denjhang/OPN-OPLL-MegaMod/OPN+OPLL AMP v0.1/pics/sshot-20231009-171946.png

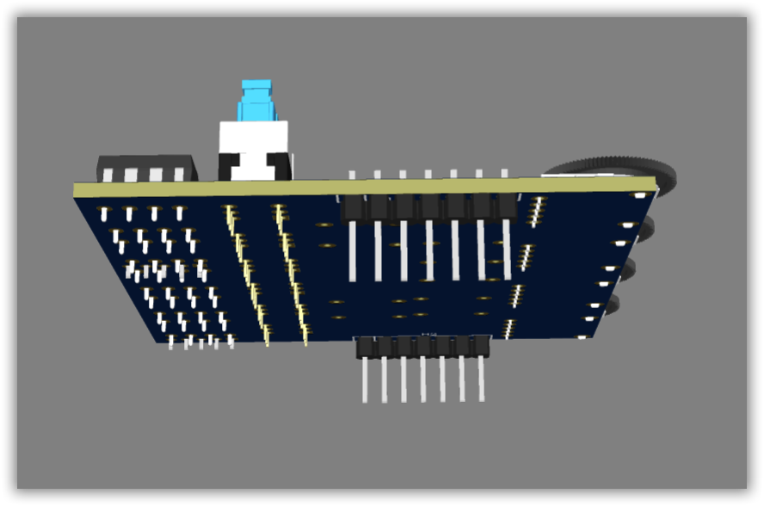
OPN+OPLL AMP v0.1/pics/sshot-20231009-171946.png
