denjhang/OPN-OPLL-MegaMod/OPN+OPLL AMP v0.1/pics/sshot-20231009-214024.png

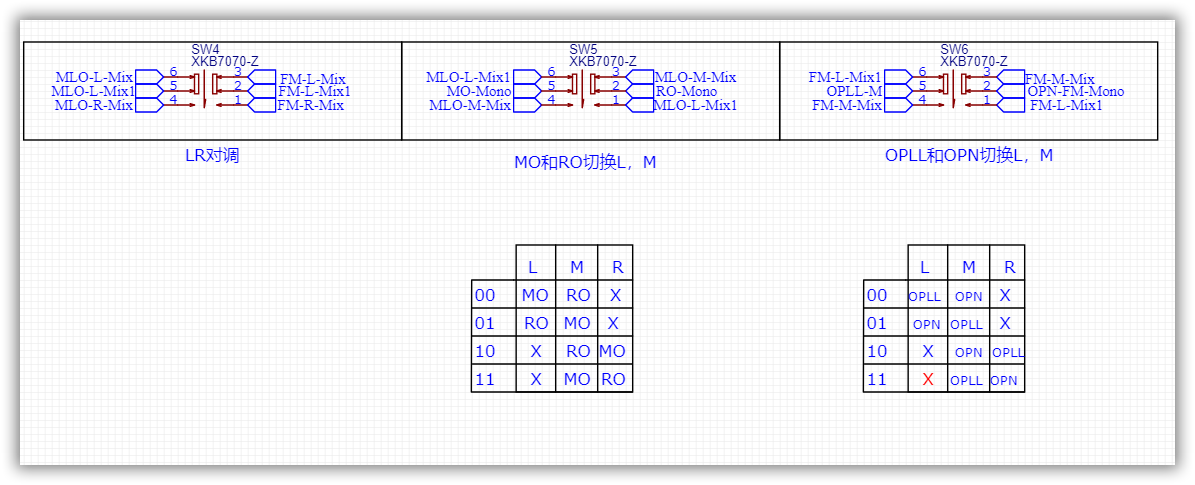
OPN+OPLL AMP v0.1/pics/sshot-20231009-214024.png
