denjhang/OPN-OPLL-MegaMod/OPN+OPLL AMP v0.1/pics/sshot-20231010-000824.png

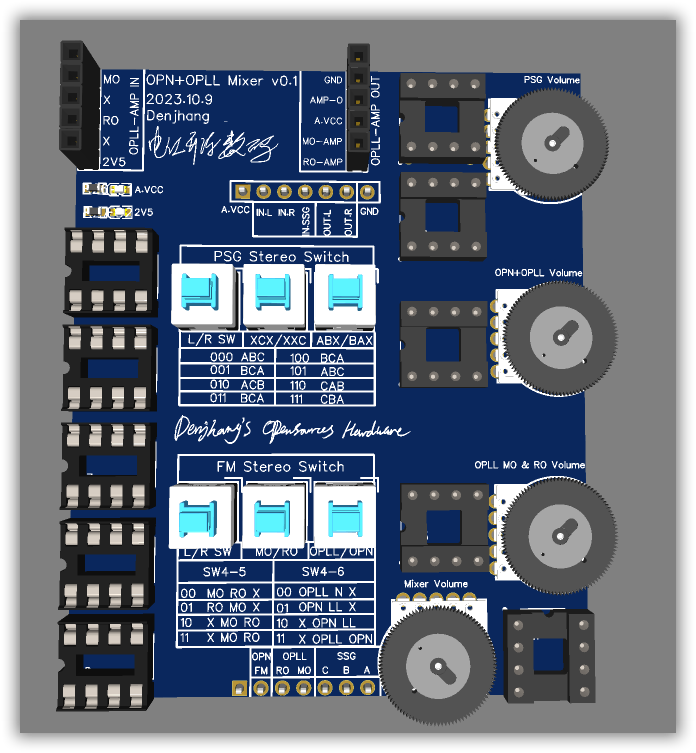
OPN+OPLL AMP v0.1/pics/sshot-20231010-000824.png
