denjhang/OPN-OPLL-MegaMod/OPN+OPLL Mixer v0.2/sshot-20231104-174121.png

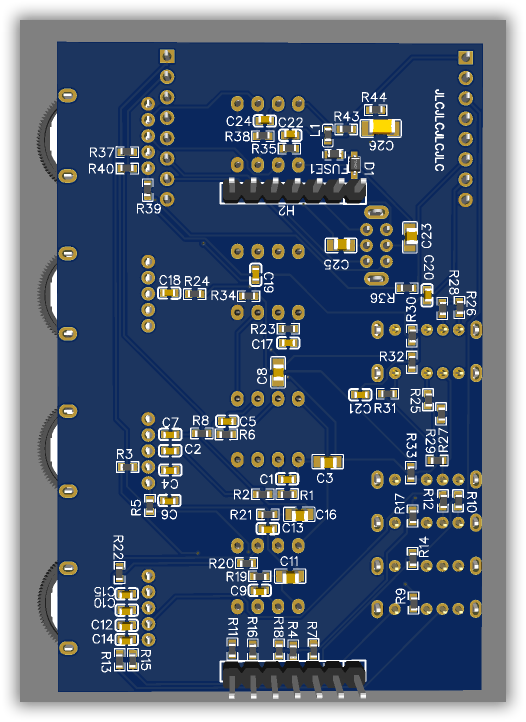
OPN+OPLL Mixer v0.2/sshot-20231104-174121.png
