denjhang/OPN-OPLL-MegaMod/pics/sshot-20231008-172245.png

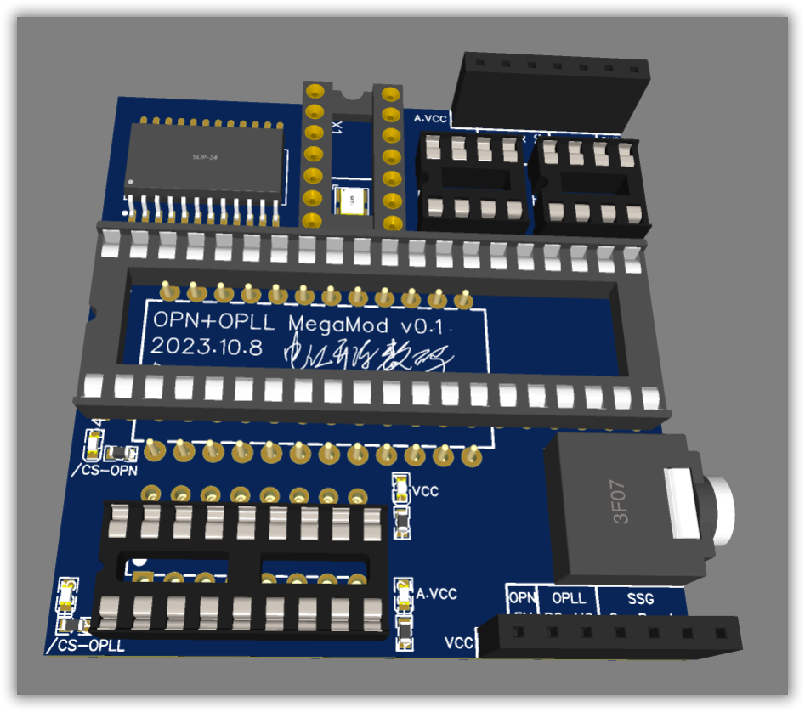
pics/sshot-20231008-172245.png
