denjhang/OPN-OPLL-MegaMod/pics/sshot-20231008-172254.png

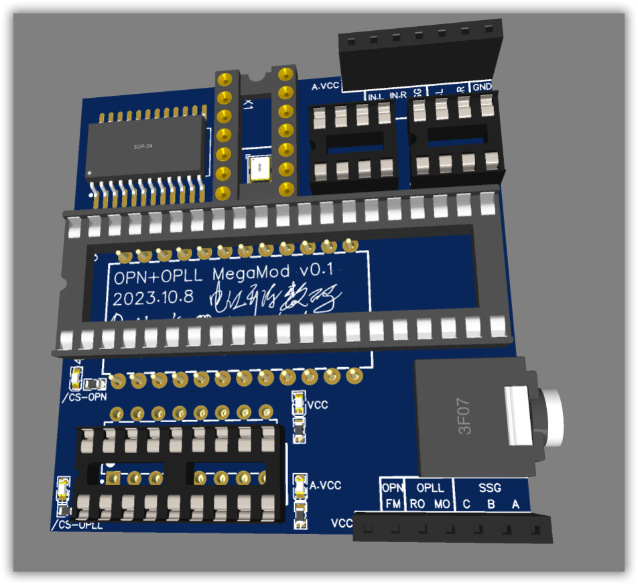
pics/sshot-20231008-172254.png
