denjhang/OPN-OPLL-MegaMod/pics/sshot-20231008-172621.png

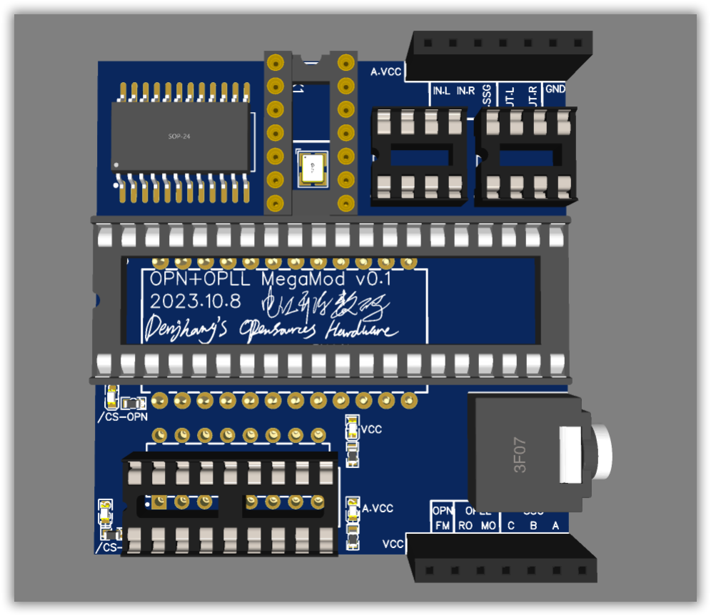
pics/sshot-20231008-172621.png
