denjhang/OPN-OPLL-MegaMod/pics/sshot-20231008-172805.png

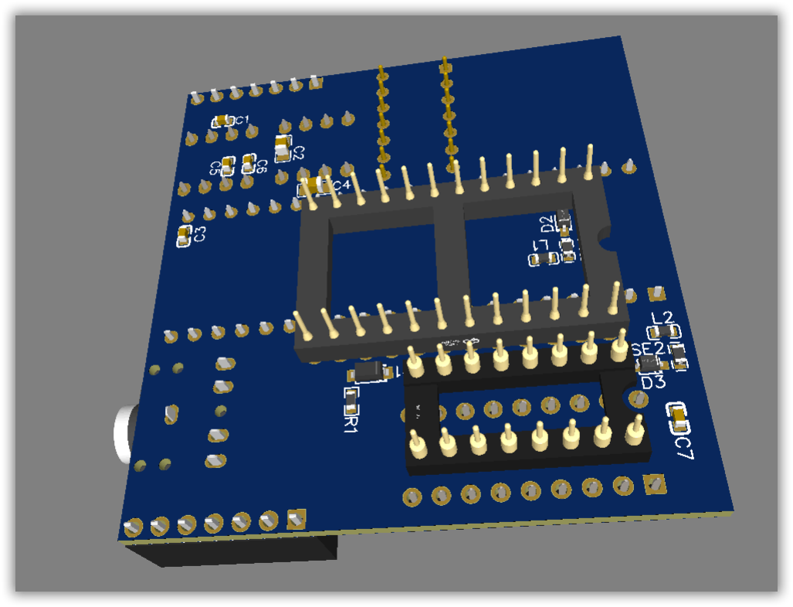
pics/sshot-20231008-172805.png
