denjhang/OPN-OPLL-MegaMod/pics/sshot-20231008-173001.png

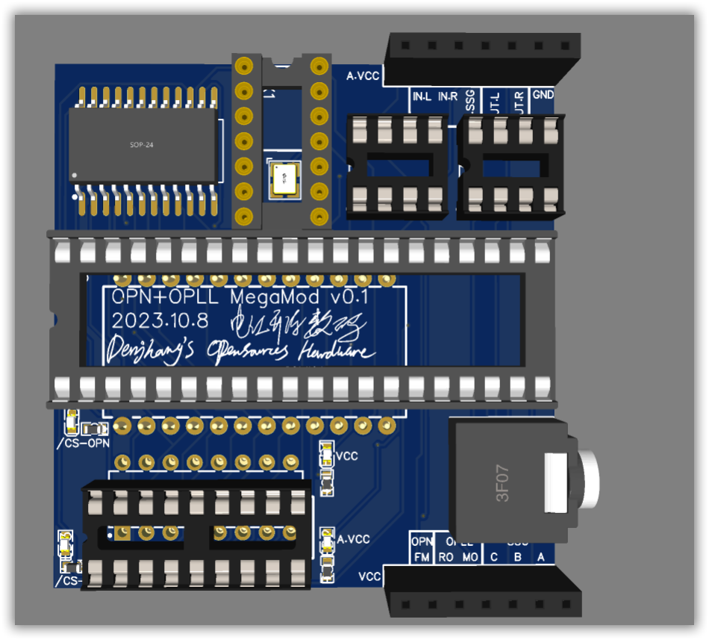
pics/sshot-20231008-173001.png
