denjhang/OPN-OPLL-MegaMod/pics/sshot-20231008-173020.png

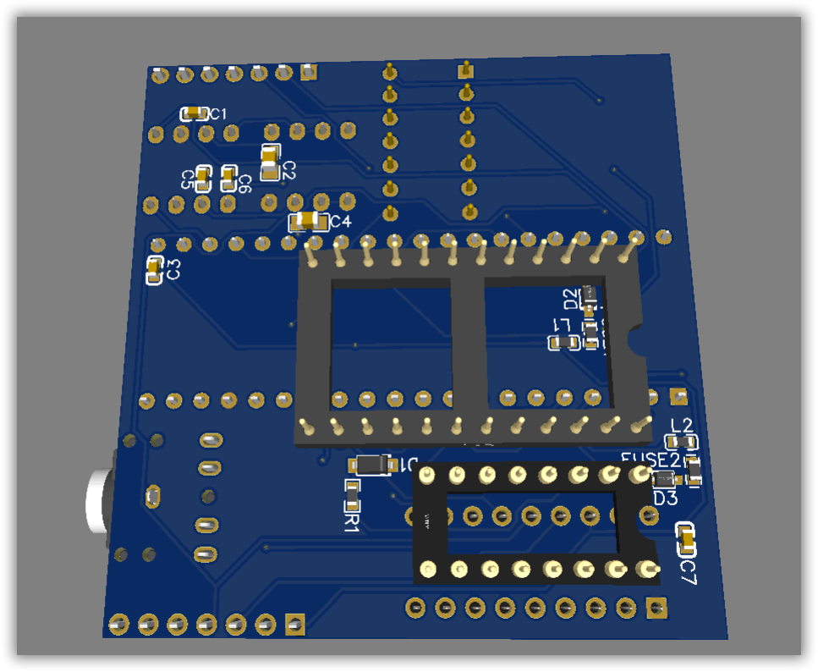
pics/sshot-20231008-173020.png
