denjhang/OPN-OPLL-MegaMod/资料2/5V 5X preamp.png

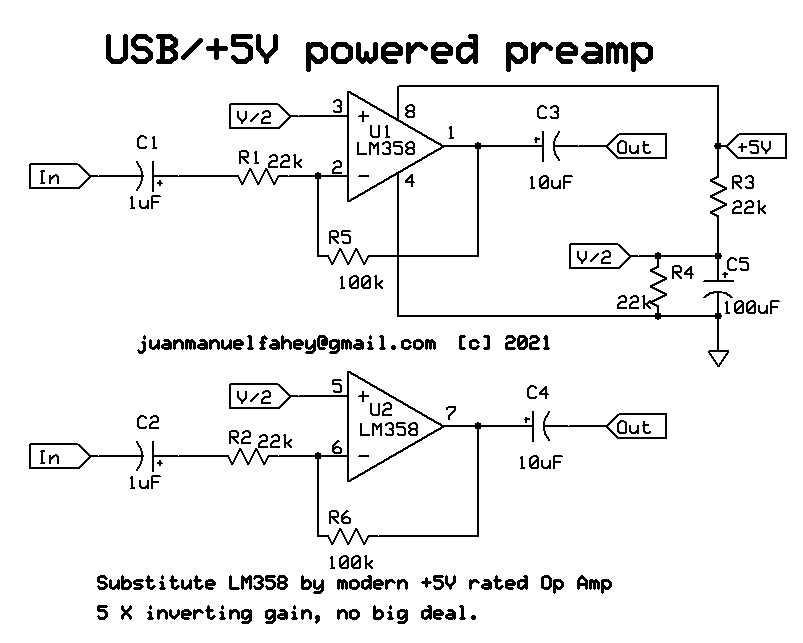
资料2/5V 5X preamp.png
