denjhang/OPN-OPLL-MegaMod/资料2/amplifier-amp112.gif

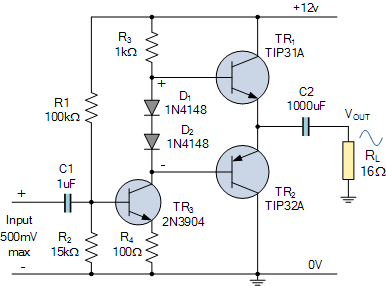
资料2/amplifier-amp112.gif
