denjhang/OPN-OPLL-MegaMod/资料2/flxtU.png

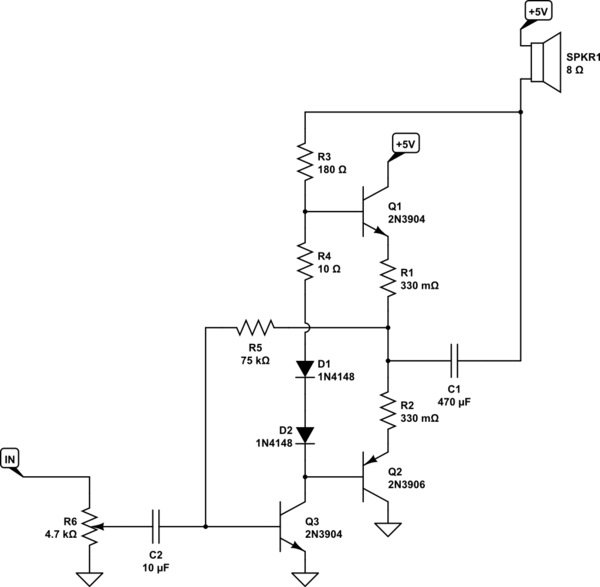
资料2/flxtU.png
