denjhang/OPN-OPLL-MegaMod/资料2/fm_hat_turbo1.0-f.jpg

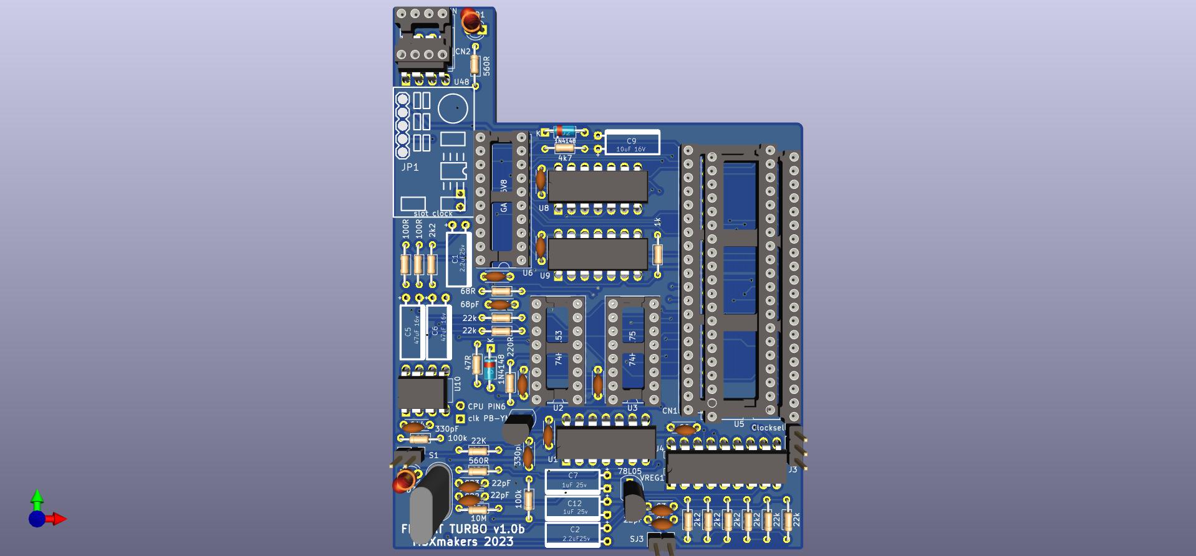
资料2/fm_hat_turbo1.0-f.jpg
