denjhang/OPN-OPLL-MegaMod/资料2/Fva4u.png

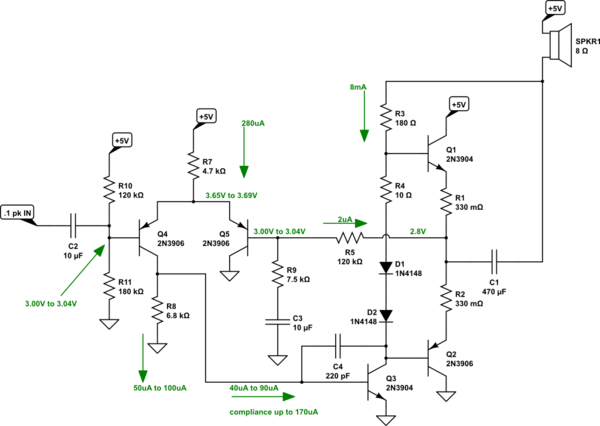
资料2/Fva4u.png
