denjhang/OPN-OPLL-MegaMod/资料2/QDV9V.jpg

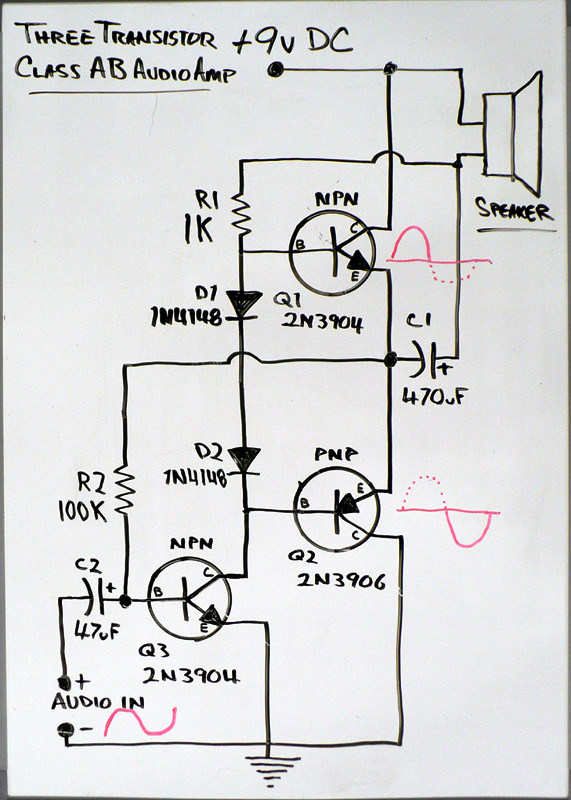
资料2/QDV9V.jpg
