denjhang/OPN-OPLL-MegaMod/资料3/6f60fb1f44.jpg

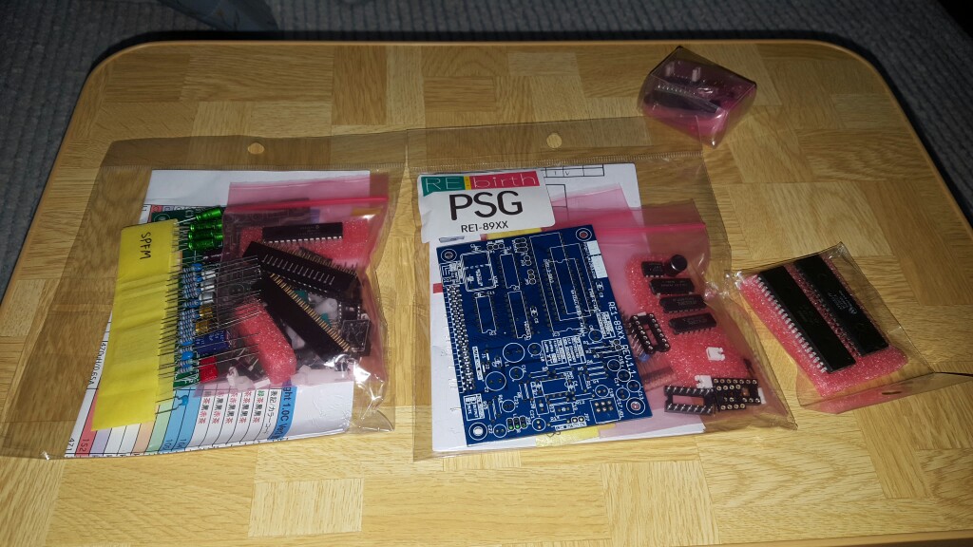
资料3/6f60fb1f44.jpg
