denjhang/OPN-OPLL-MegaMod/资料3/0962512435.jpg

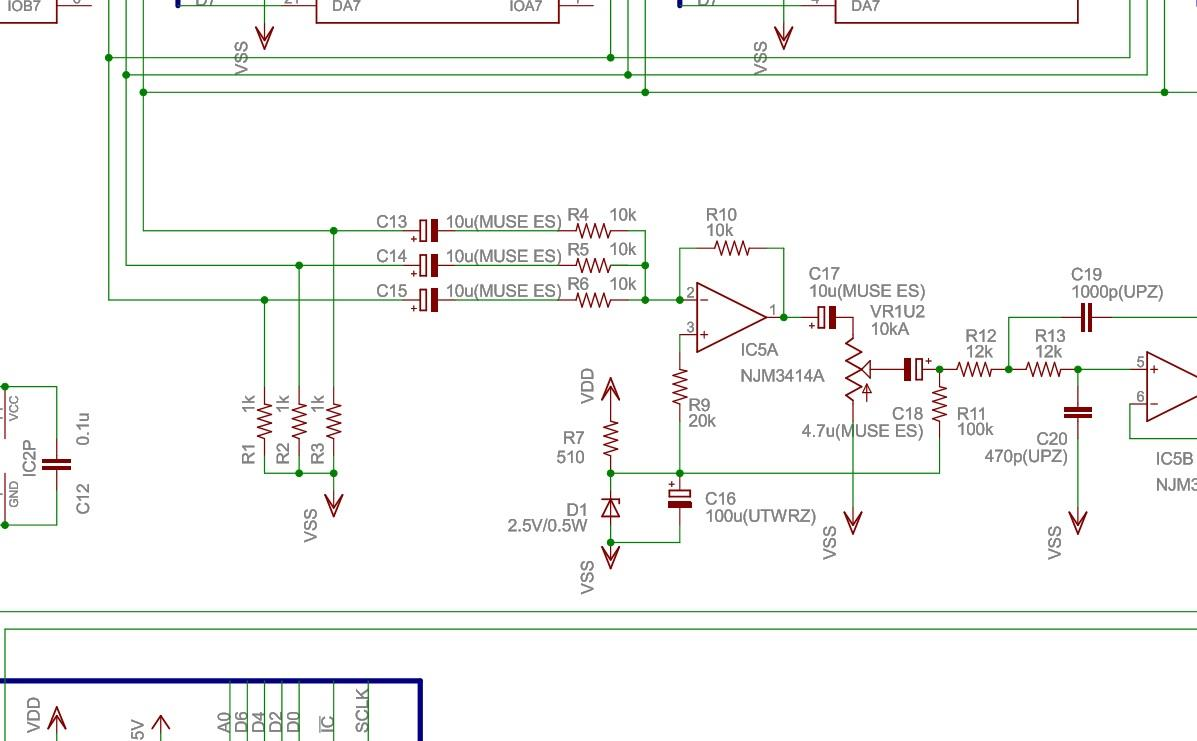
资料3/0962512435.jpg
