denjhang/OPN-OPLL-MegaMod/资料3/eye_RE1-Y8950-800x450.jpg

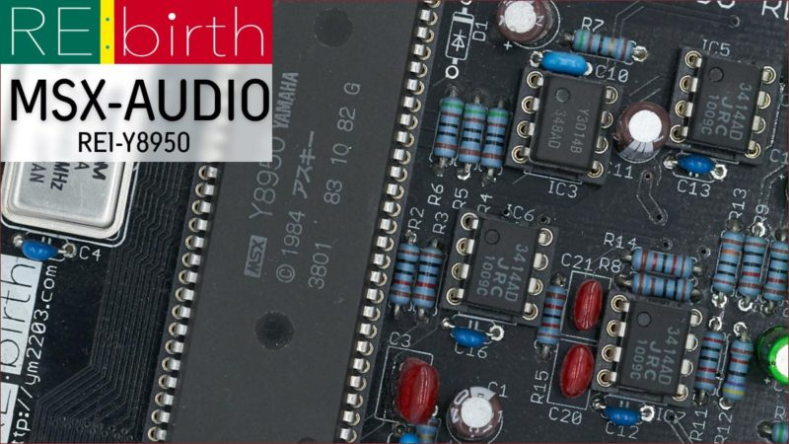
资料3/eye_RE1-Y8950-800x450.jpg
