denjhang/OPN-OPLL-MegaMod/资料3/ffea17fb9c (1).jpg

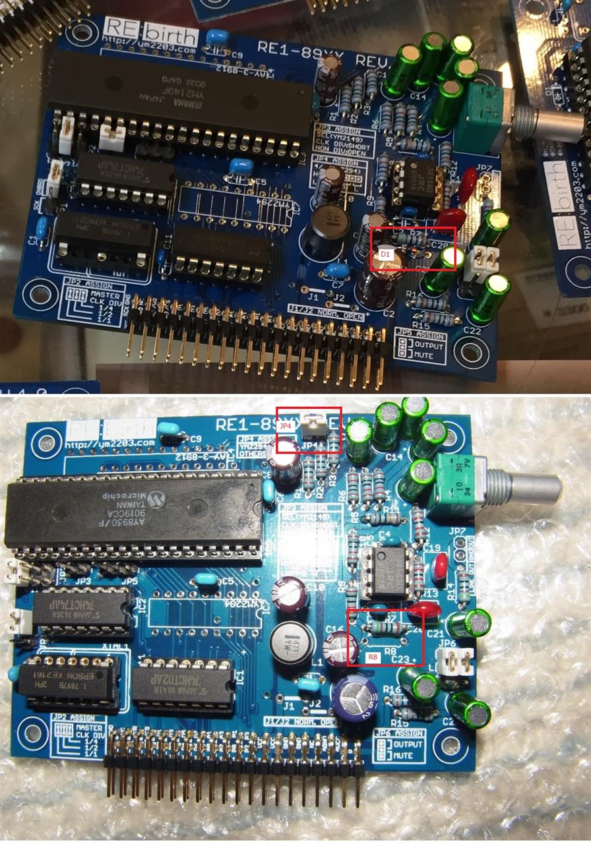
资料3/ffea17fb9c (1).jpg
