denjhang/OPN-OPLL-MegaMod/资料3/l3psg6n9_sch1.png

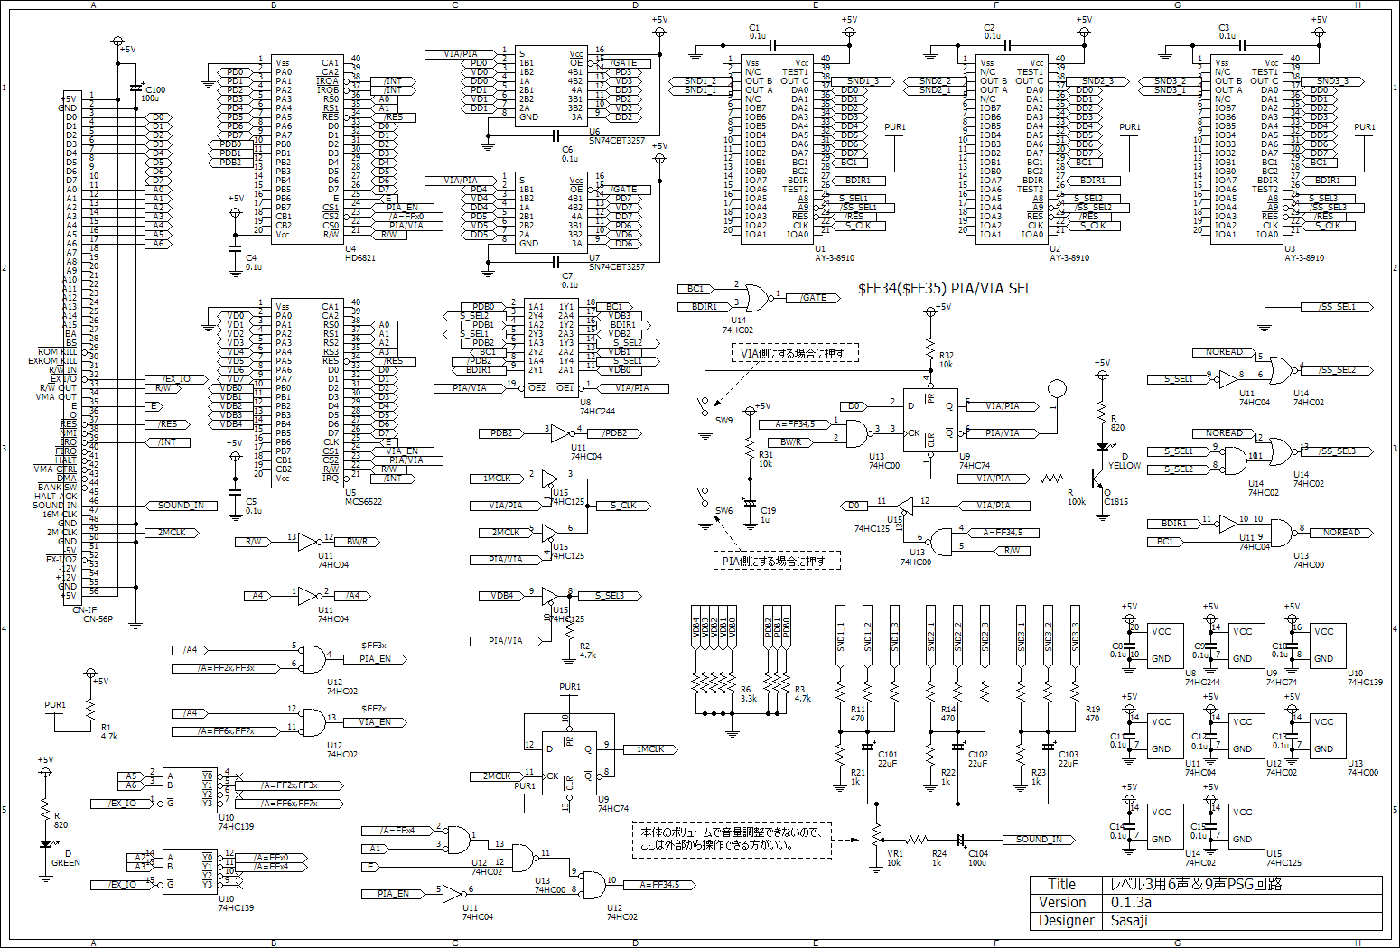
资料3/l3psg6n9_sch1.png
