denjhang/OPN-OPLL-MegaMod/资料3/l1040789603.5.jpg

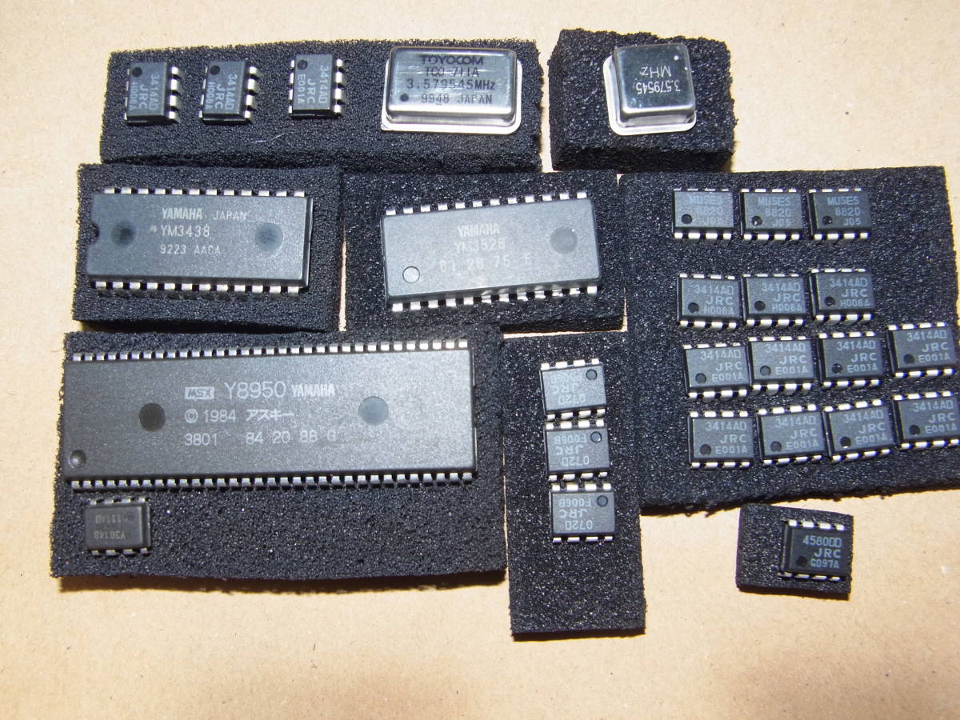
资料3/l1040789603.5.jpg
