denjhang/OPN-OPLL-MegaMod/资料3/mc3-io-ym2413-sch.png

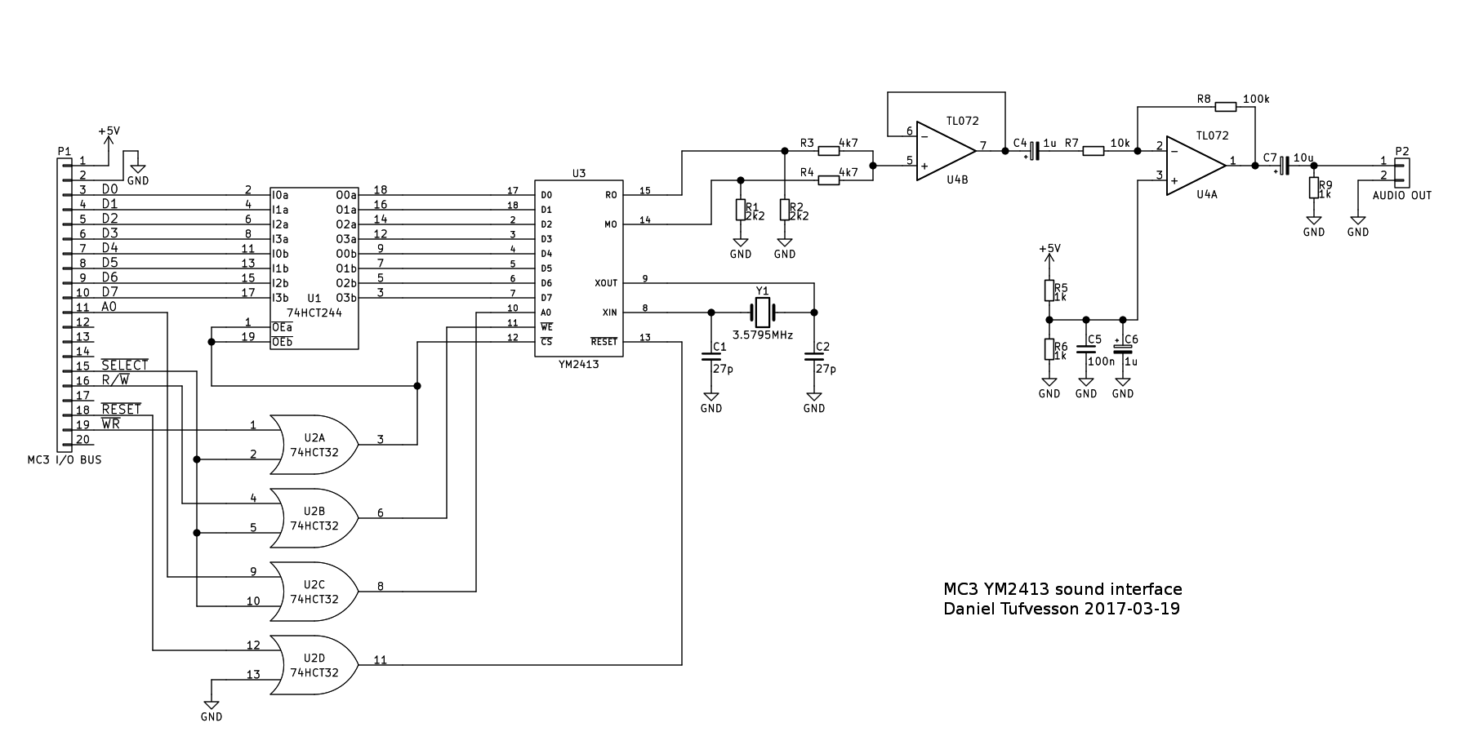
资料3/mc3-io-ym2413-sch.png
