denjhang/OPN-OPLL-MegaMod/资料3/pss_460_lfo_and_bbd_160_133.gif

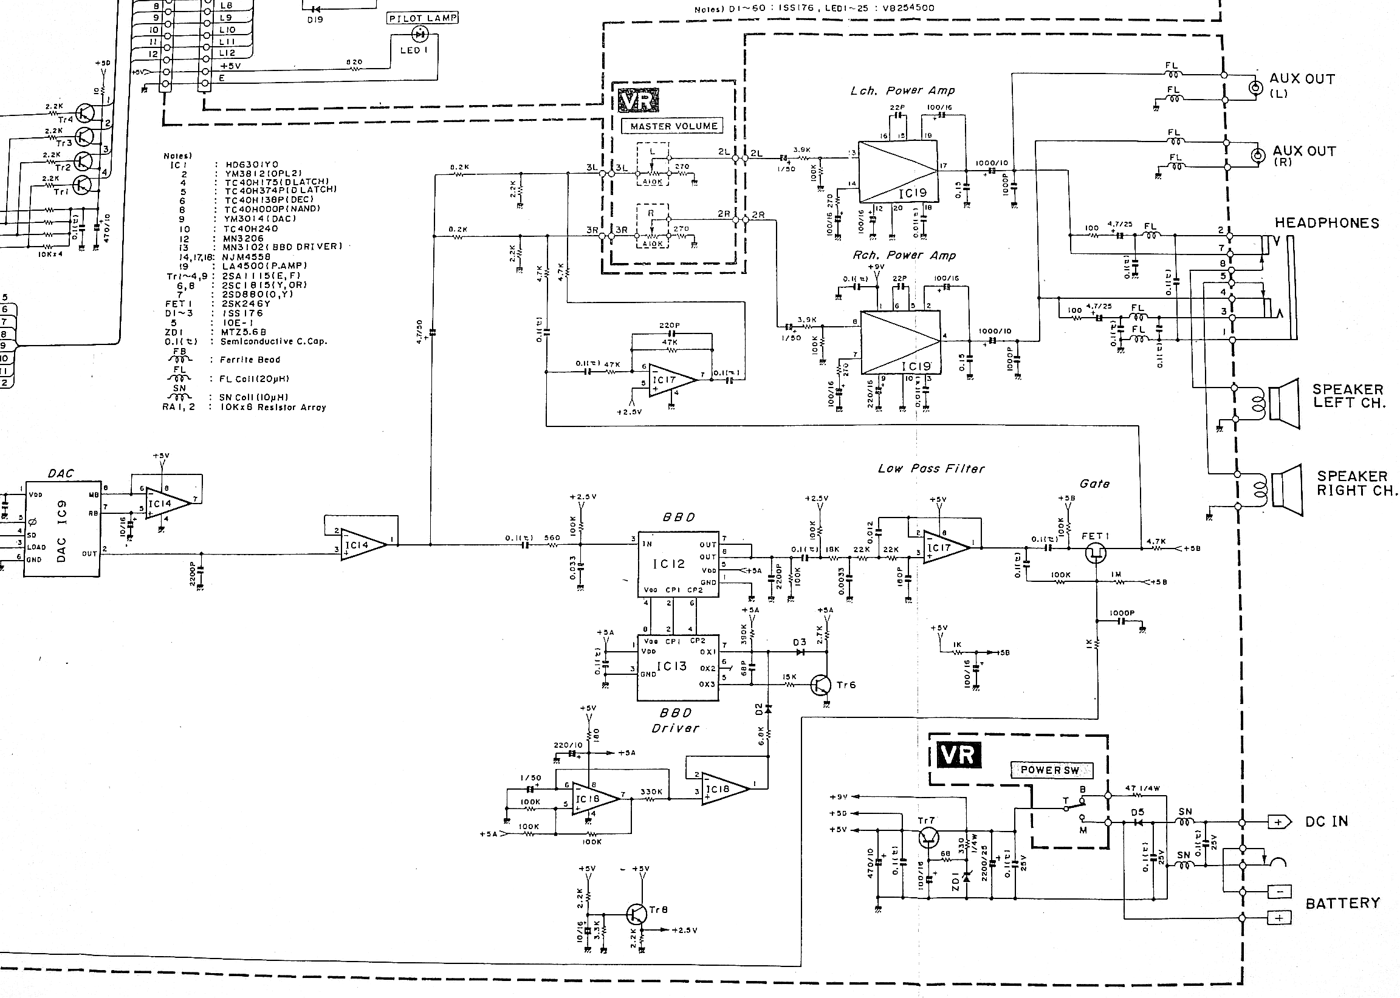
资料3/pss_460_lfo_and_bbd_160_133.gif
