denjhang/OPN-OPLL-MegaMod/资料3/RE1-Y8950_2.jpg

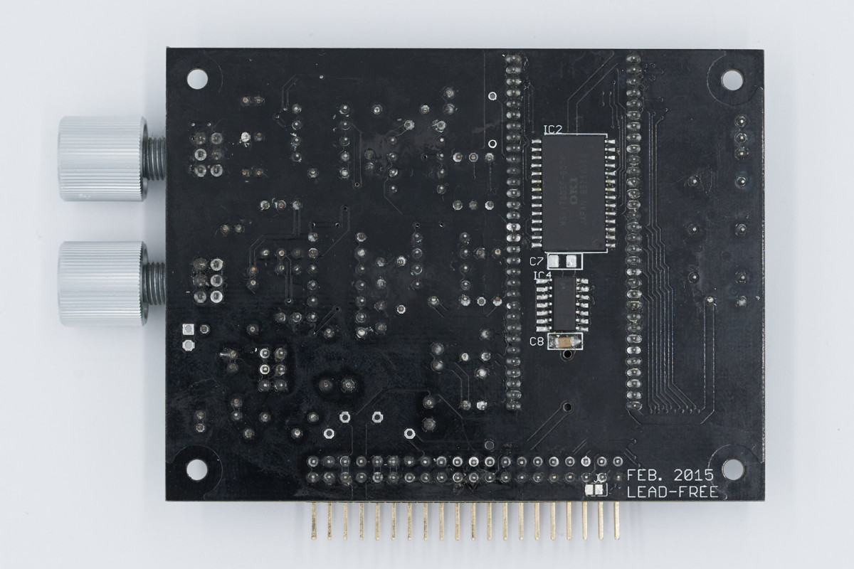
资料3/RE1-Y8950_2.jpg
