denjhang/OPN-OPLL-MegaMod/资料/fmpac.png

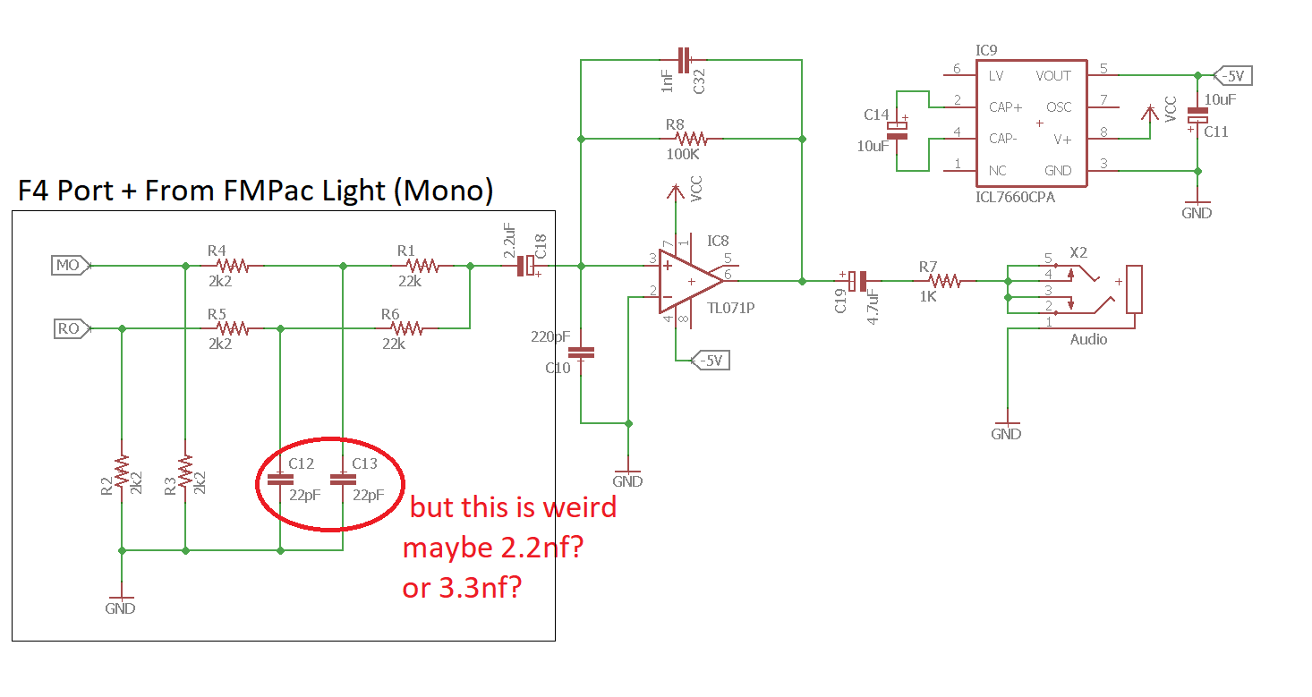
资料/fmpac.png
