denjhang/OPN-OPLL-MegaMod/资料/Opamp_output (1).jpg

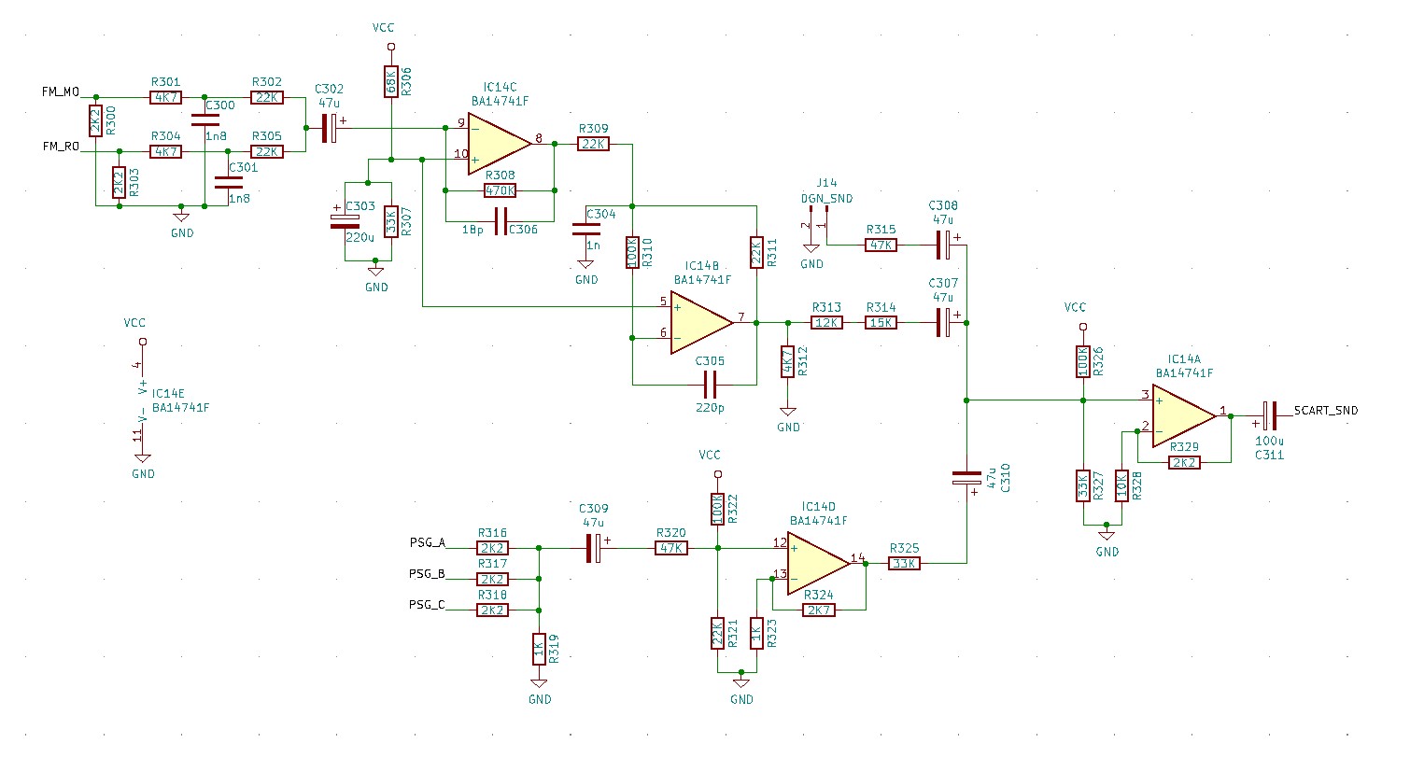
资料/Opamp_output (1).jpg
