denjhang/OPN-OPLL-MegaMod/资料/Panasonic_FS_A1WX_Audio.png

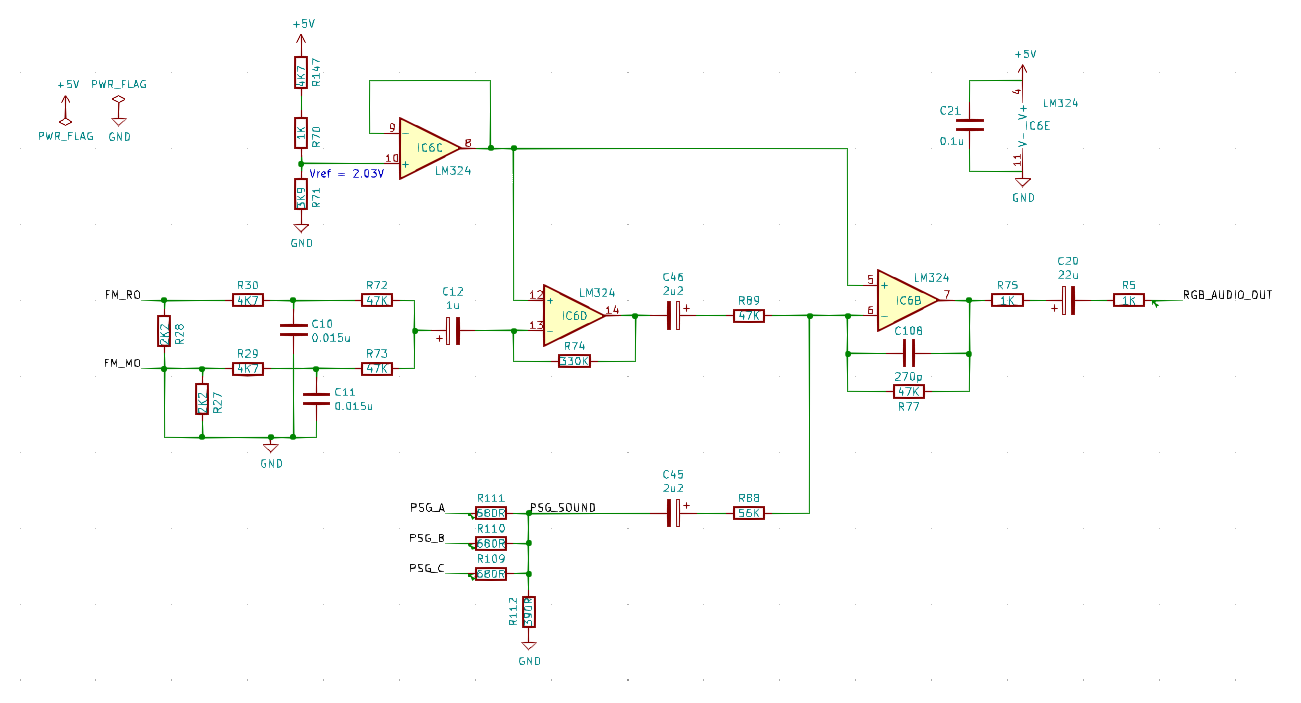
资料/Panasonic_FS_A1WX_Audio.png
