denjhang/OPN-OPLL-MegaMod/资料/pin_out - 副本.gif

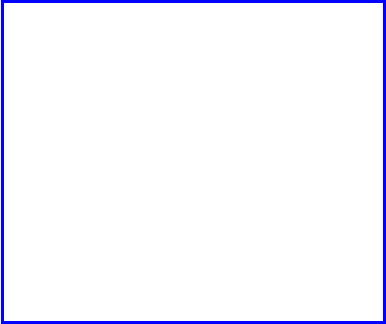
资料/pin_out - 副本.gif
