denjhang/OPN-OPLL-MegaMod/资料/pin_out - 副本.jpg

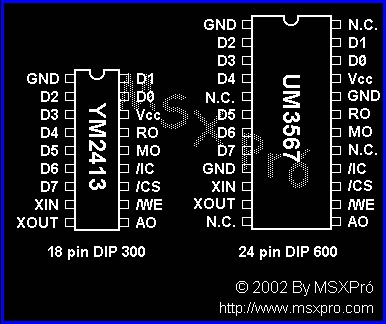
资料/pin_out - 副本.jpg
