denjhang/OPN-OPLL-MegaMod/资料3/ecb-vgm-001c.pdf

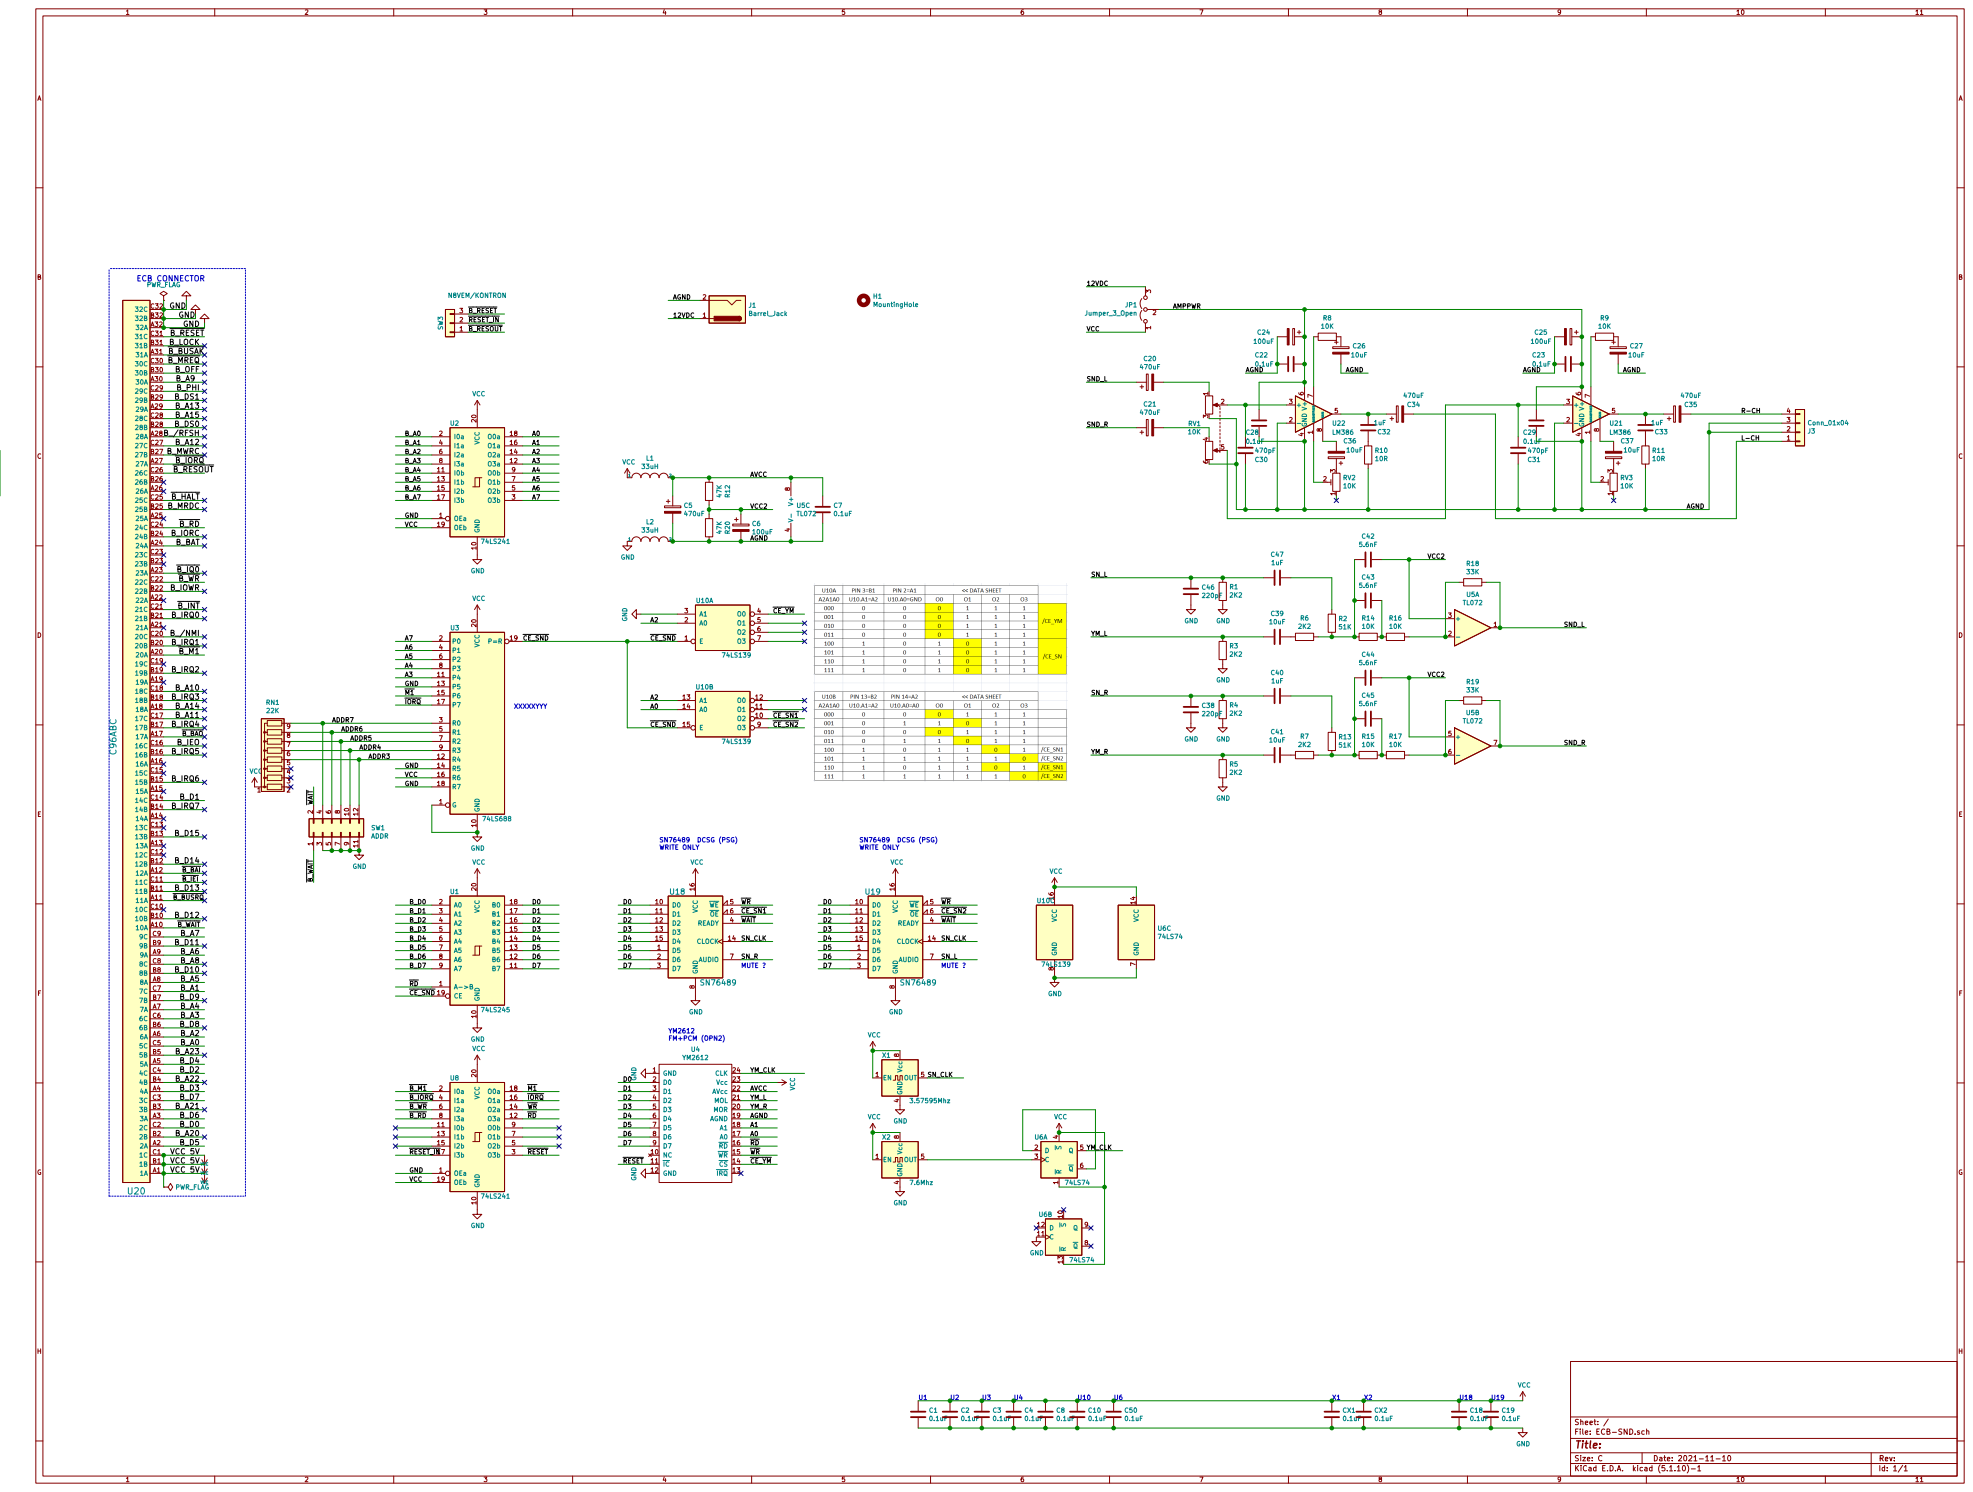
[picture p209: page 1]

B_RESET
B_LOCK

SN76489 DCSG (PSG) WRITE ONLY

8 U19 SN76489 D5 1 D0 10 D1 11 D2 12 D3 13 CLOCK 14 D4 15 VCC 16 D6 2 D7 3 READY 4 WE 5 OE 6 AUDIO 7 GND

Id: 1/1 Title: File: ECB-SND.sch Sheet: /
