denjhang/OPN-OPLL-MegaMod/资料3/SCH_rc2014-ym2149_2023-11-10.pdf

# O5 10 O4 11 O3 12 O2 13 O1 14 O0 15

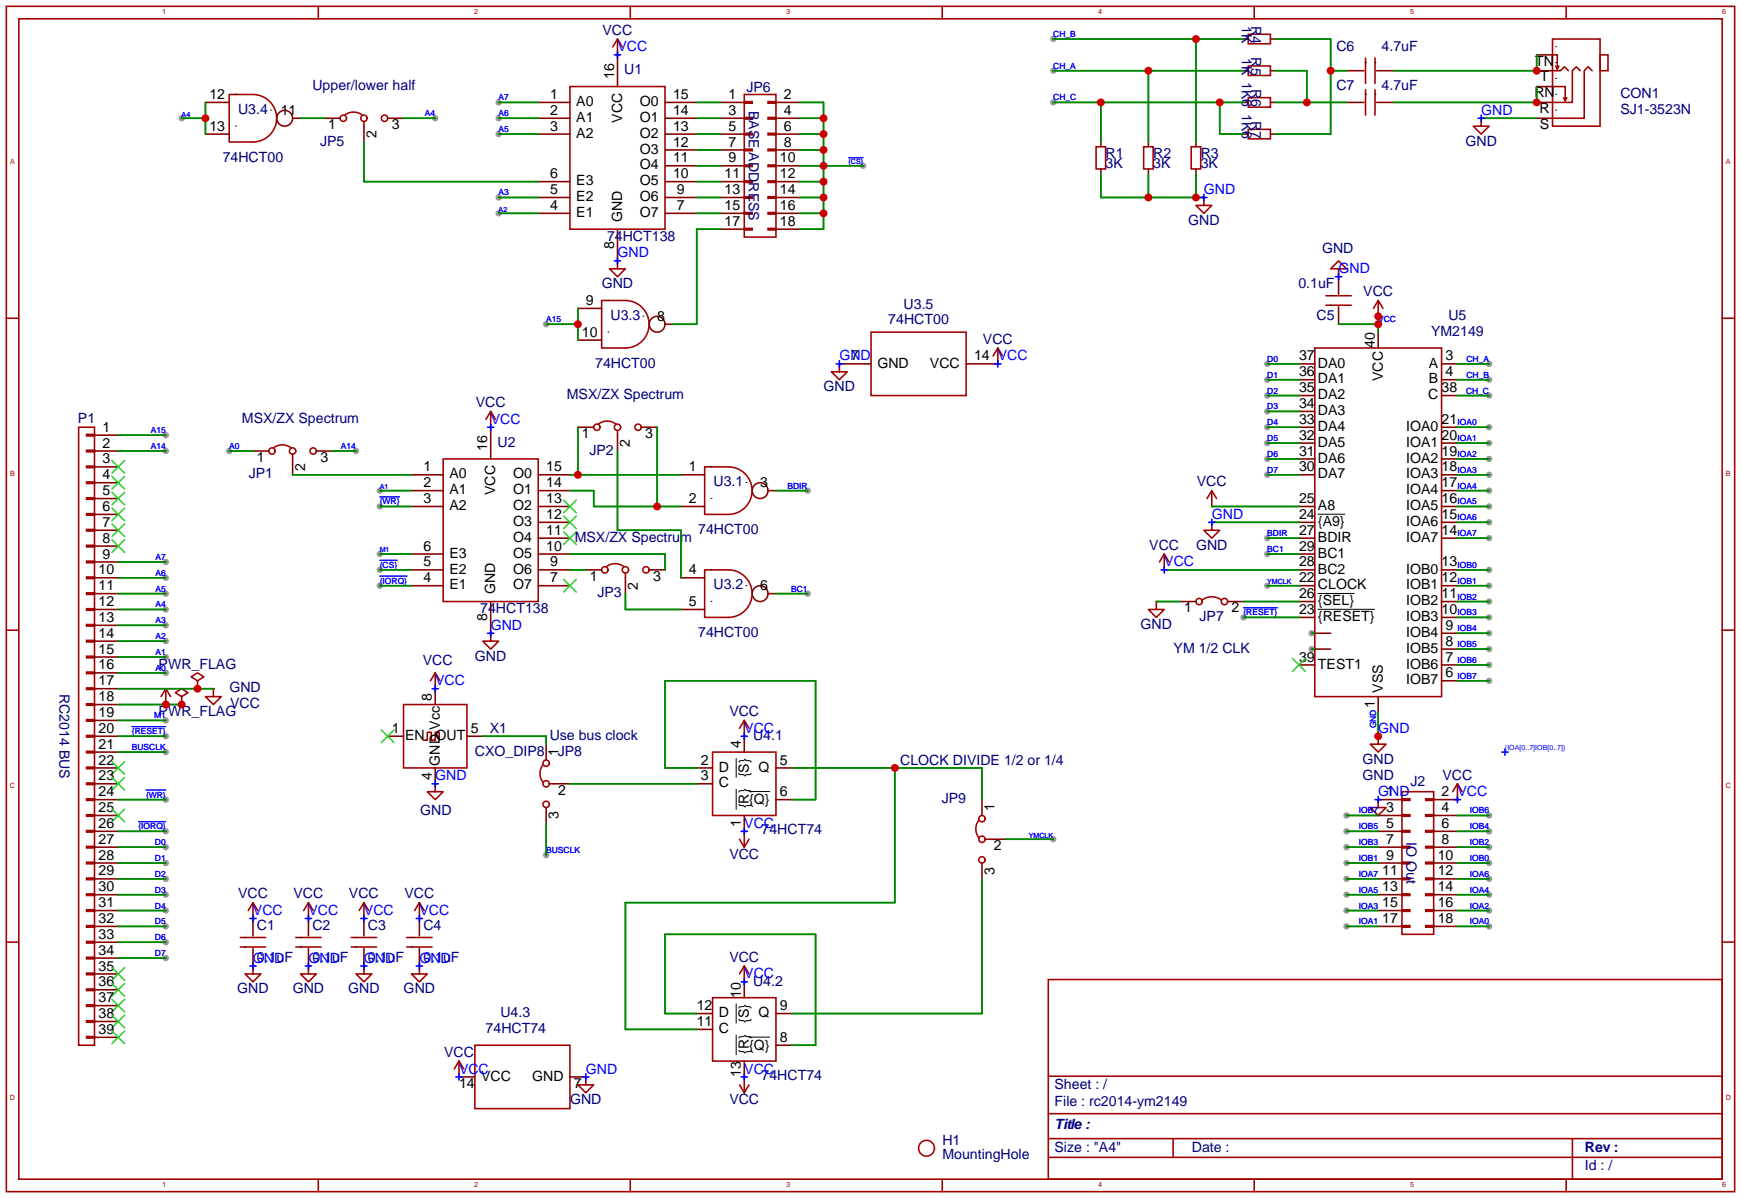
[picture p233: page 1]
