denjhang/OPN-OPLL-MegaMod/OPN+OPLL MegaMod v0.1/Schematic_OPN+OPLL MegaMod v0.1_2023-10-08.pdf

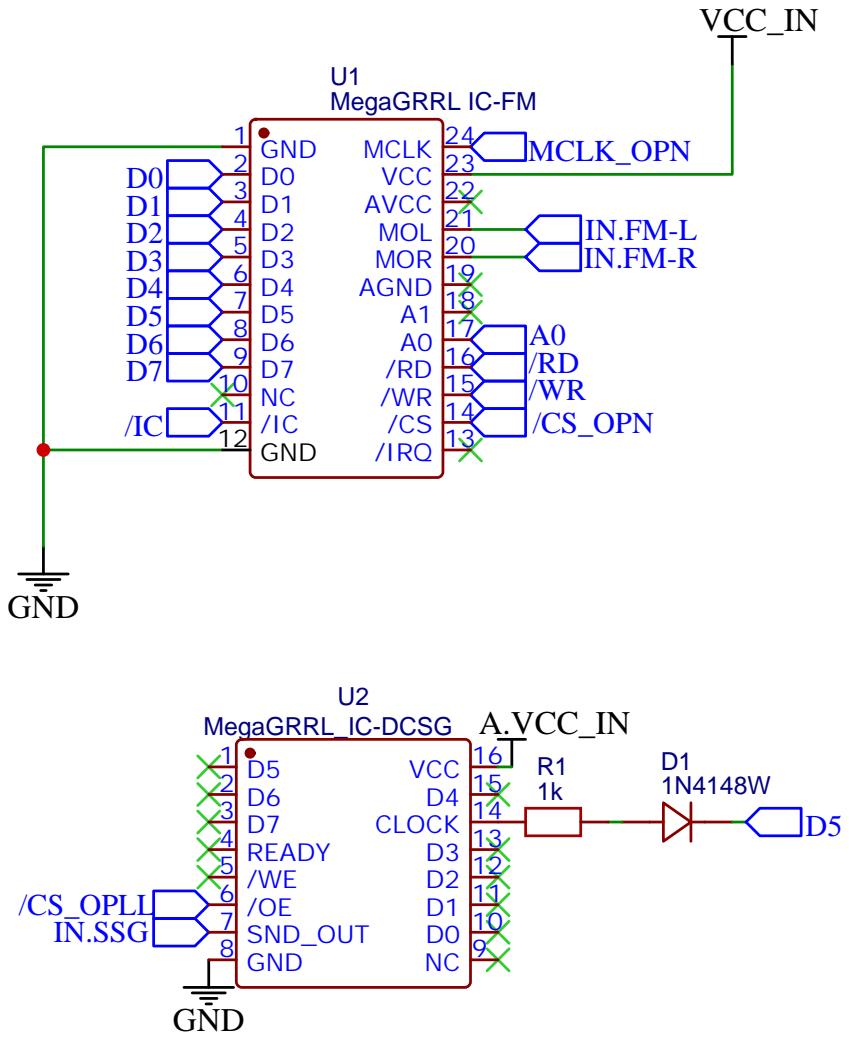
[picture p234: page 1]

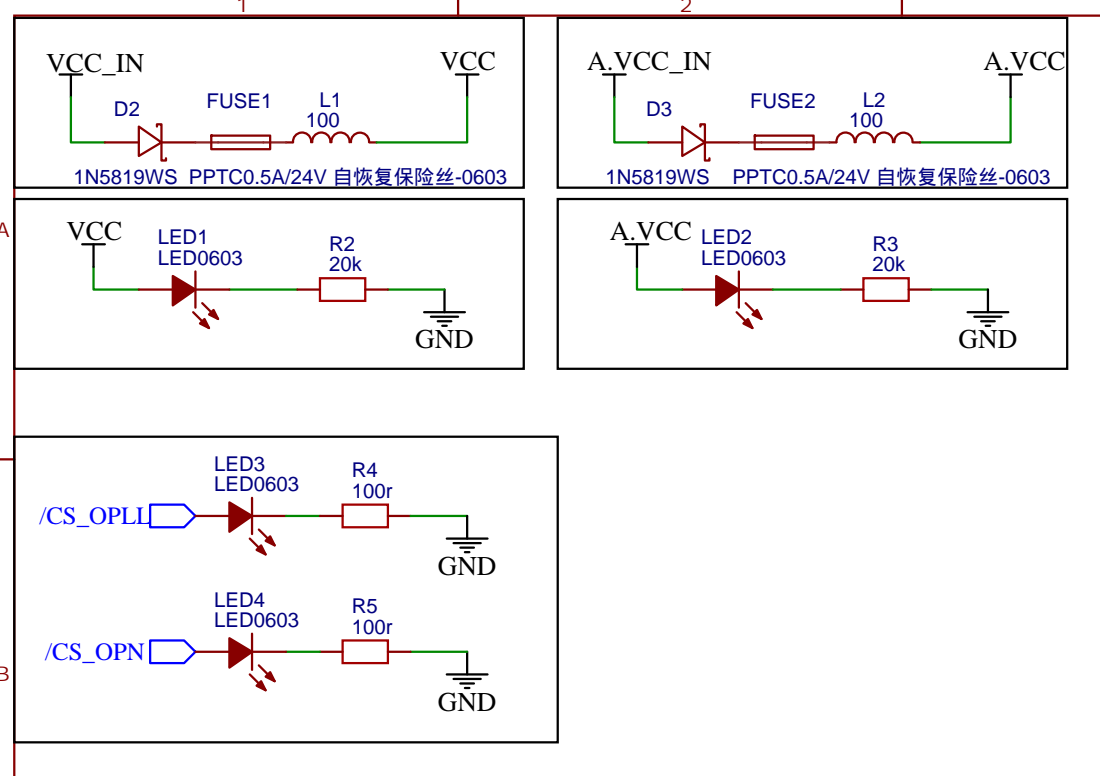
[picture p235: page 2]

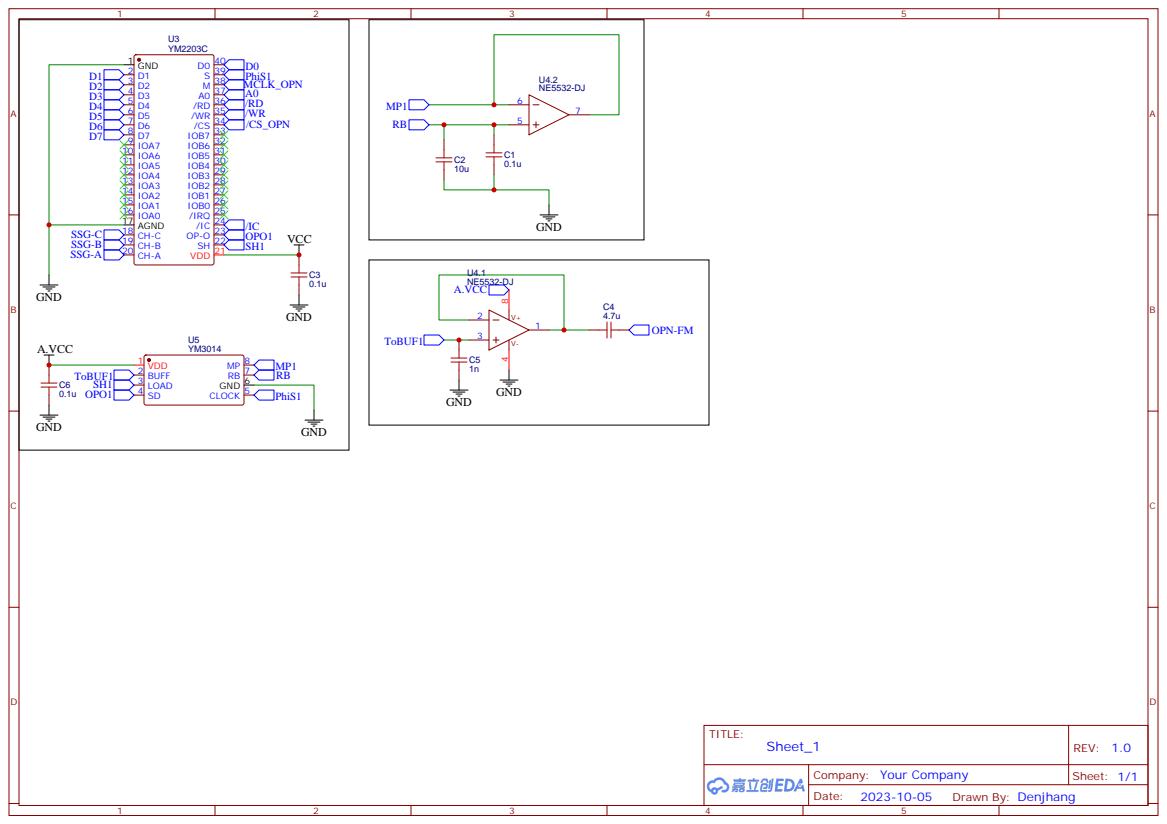
[picture p236: page 3]

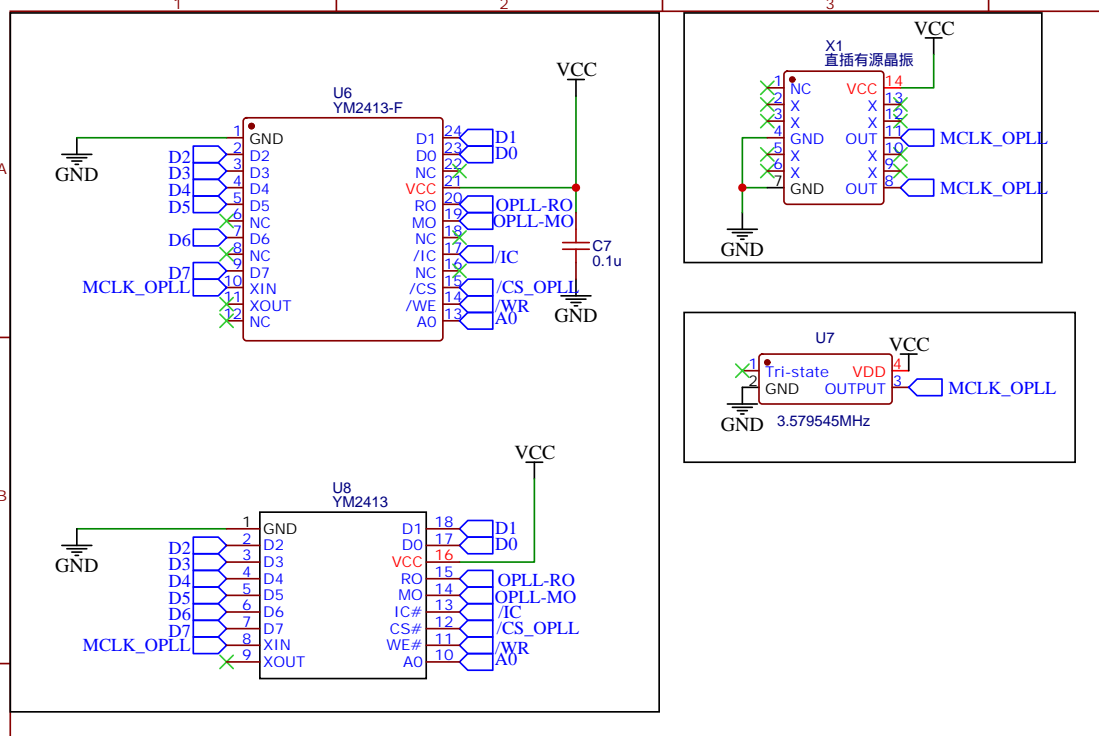
[picture p237: page 4]

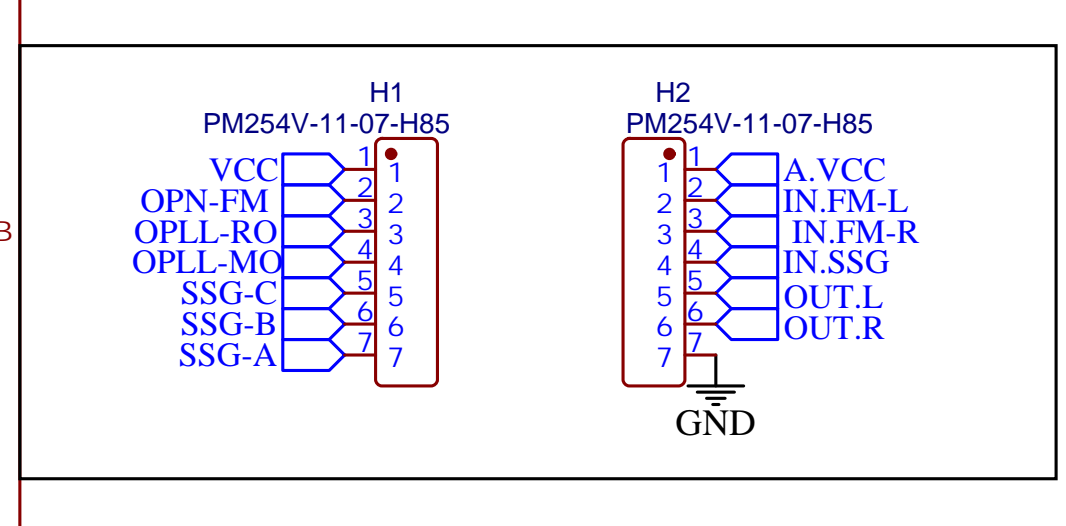
[picture p238: page 5]

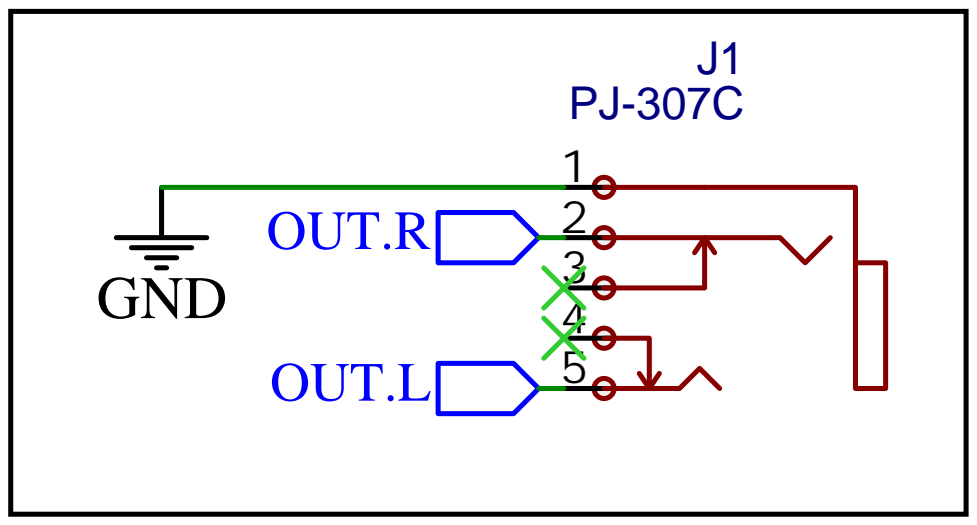
[picture p239: page 6]
