denjhang/OPN-OPLL-MegaMod/OPN+OPLL MegaMod v0.2/Schematic_OPN+OPLL MegaMod v0.2_2023-10-23.pdf

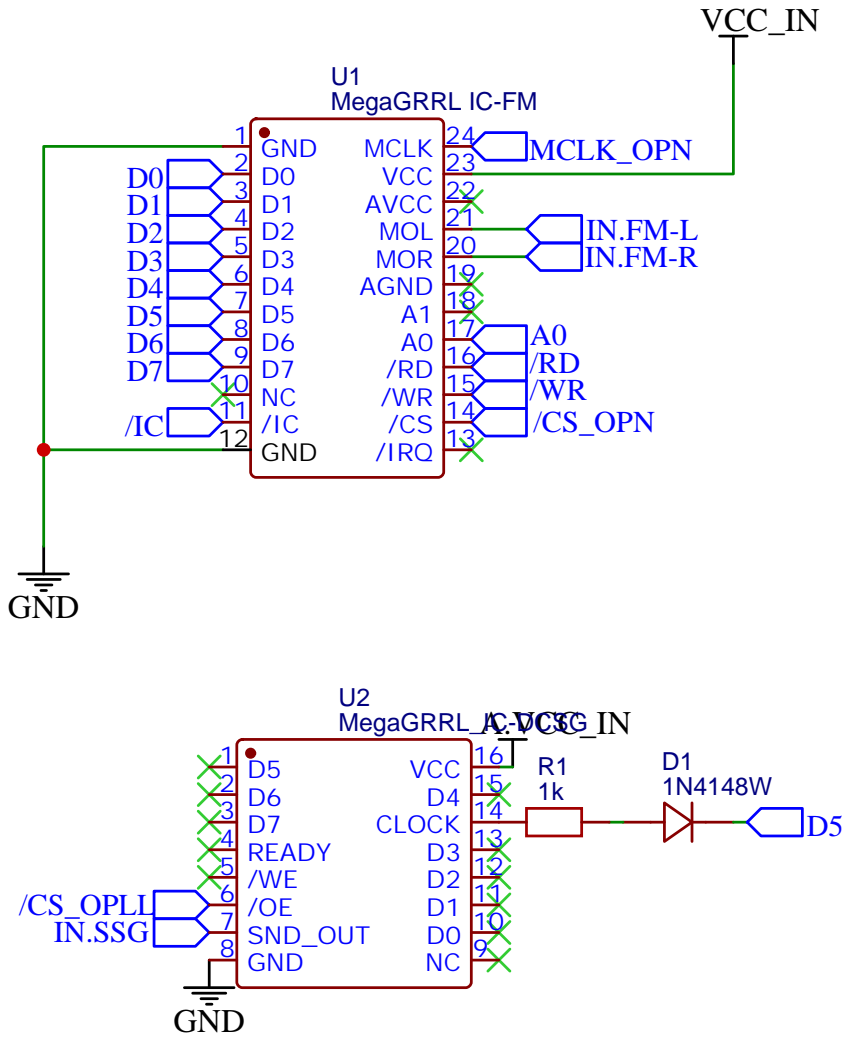
[picture p240: page 1]

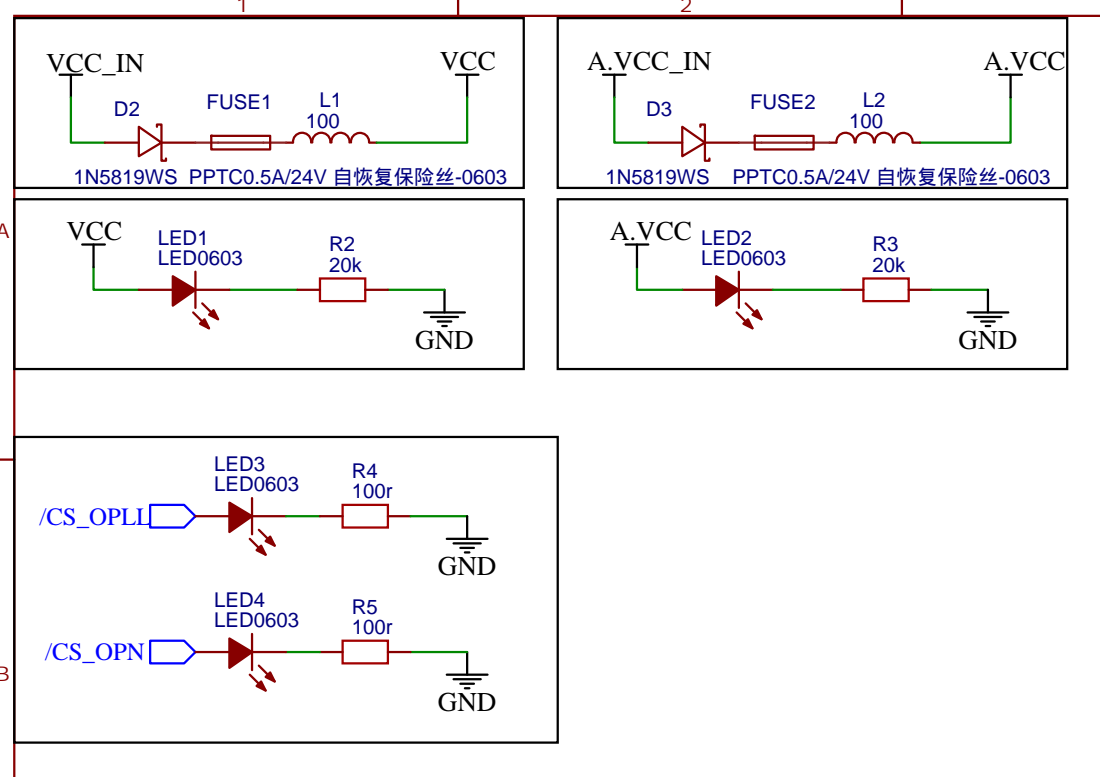
[picture p241: page 2]

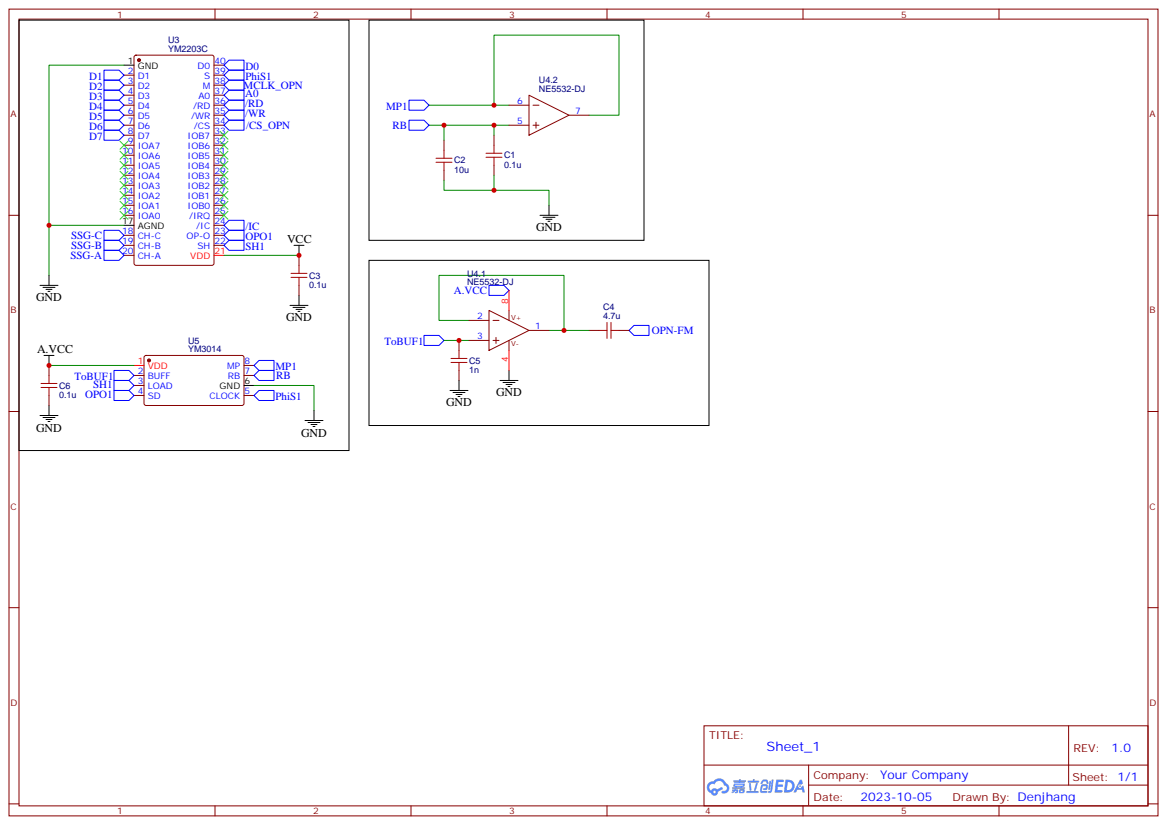
[picture p242: page 3]

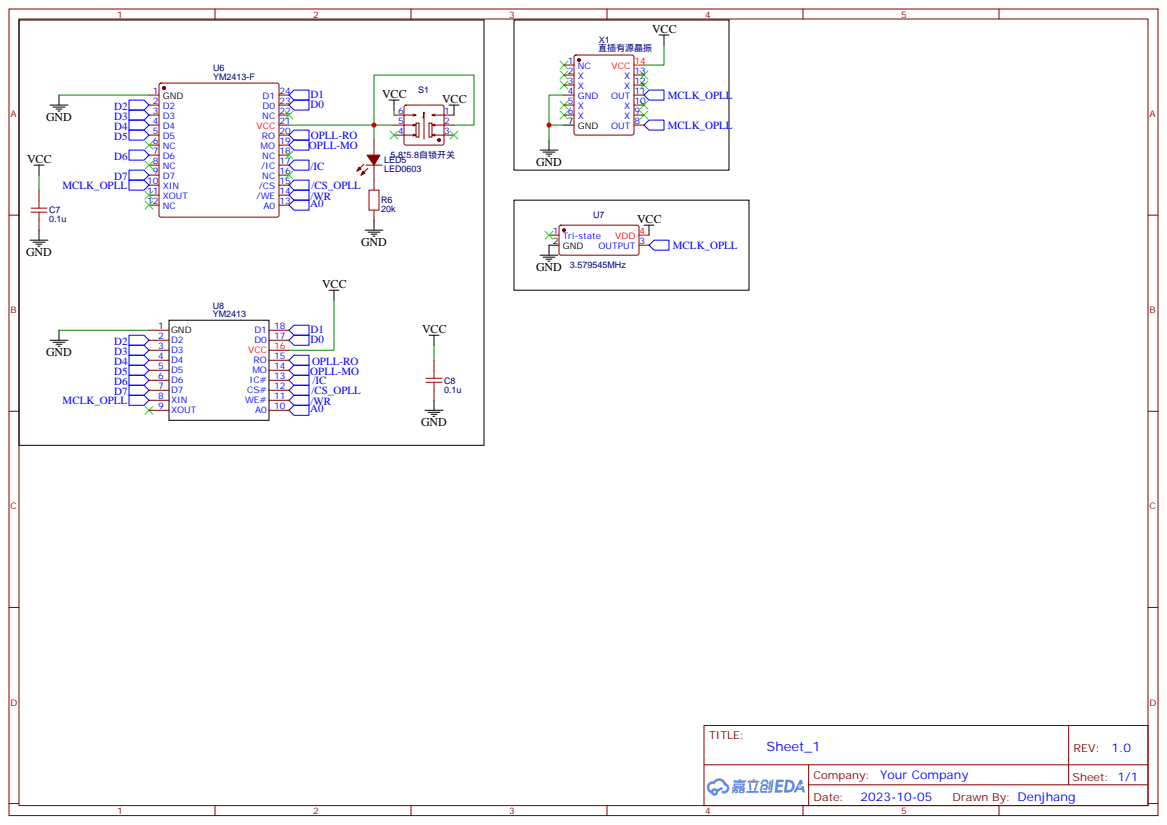
[picture p243: page 4]

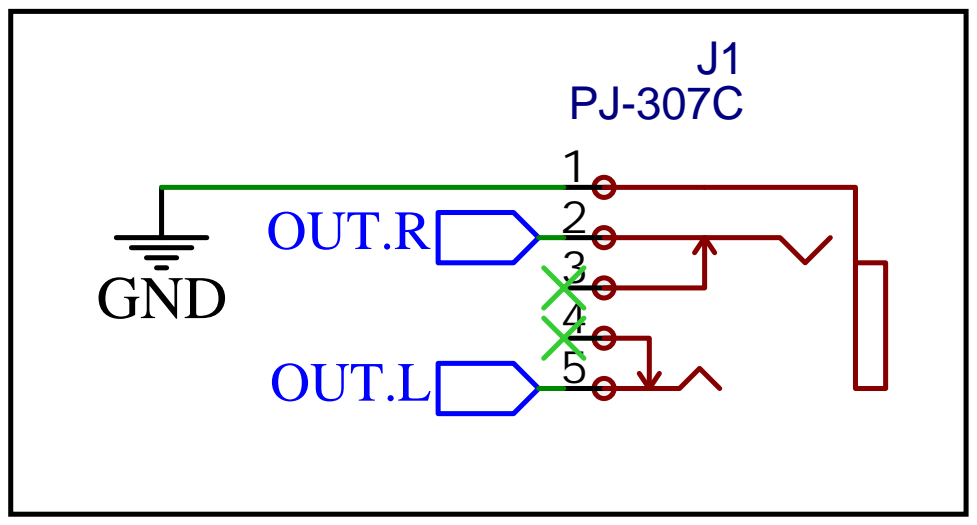
[picture p244: page 5]

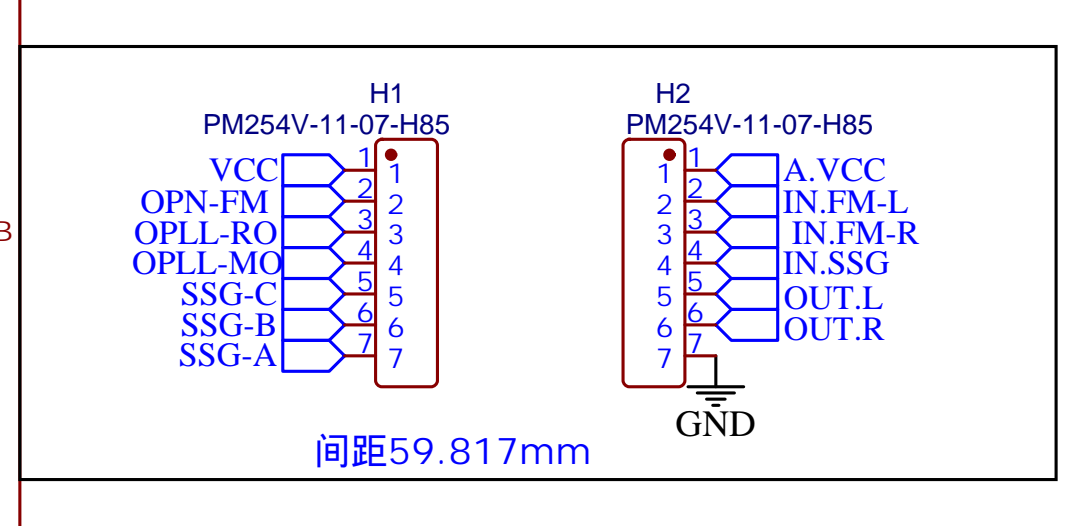
[picture p245: page 6]
